Northwest69/Hamster/Processing/Hamster/application.linux-armv6hf/source/Hamster.pde

/* Hamster
 Software: 1.0.0
 Created by Peter Chau
 Start Date: August 9, 2015
 */

import processing.serial.*;
import controlP5.*; // For GUI interface

Serial myPort;

int index;

// GUI Declarations
ControlP5 myControls;
Slider dutySlider, degreeSlider;
Textfield attemptsTextfield, maxTextfield, probabilityTextfield;

int dutyCycle = 75;
public float rotateDegree = 30;
public String probabilities = "0.16667 0.16667 0.16667 0.16667 0.16667 0.16667";

int[] dutyCycleSlider = {
  250, 50
};
int[] rotateDegreeSlider = {
  300, 50
};

String attempts = "0";
String maxAttempts = "500";
int[] learningAttempt = {
  400, 100
};
int[] maxAttempt = {
  400, 50
};

int[] probability = {
  50, 250
};

int[] forward = {
  100, 50
};
int[] backward = {
  100, 150
};
int[] left = {
  50, 100
};
int[] right = {
  150, 100
};
int[] stop = {
  100, 100
};
int[] set = {
  400, 150
};
int[] reset = {
  400, 175
};
int[] save = {
  350, 250
};
int[] load = {
  400, 250
};

int foreground = #FF8686;
int background = #AA0000;
int active = #FF2929;
int canvas = #FFB2B2;

void setup() {
  String portName = Serial.list()[1]; //1 is bluetooth, 2 is serial
  myPort = new Serial(this, portName, 38400);
  myPort.clear();

  size(500, 350);
  background(100);

  /* GUI interface */
  myControls = new ControlP5(this);
  dutySlider = myControls.addSlider("dutyCycle", 0, 100, dutyCycle, dutyCycleSlider[0], dutyCycleSlider[1], 10, 137).setColorForeground(foreground).setColorActive(active).setColorBackground(background);
  degreeSlider = myControls.addSlider("rotateDegree", 1, 360, rotateDegree, rotateDegreeSlider[0], rotateDegreeSlider[1], 10, 137).setColorForeground(foreground).setColorActive(active).setColorBackground(background);
  maxTextfield = myControls.addTextfield("Max Attempts").setPosition(maxAttempt[0], maxAttempt[1]).setText(maxAttempts).setSize(50, 25).setAutoClear(false).setColorForeground(foreground).setColorActive(active).setColorBackground(background);
  attemptsTextfield = myControls.addTextfield("Current Attempts").setPosition(learningAttempt[0], learningAttempt[1]).setText(attempts).setSize(50, 25).setAutoClear(false).setColorForeground(foreground).setColorActive(active).setColorBackground(background);
  probabilityTextfield = myControls.addTextfield("Probabilities").setPosition(probability[0], probability[1]).setText(probabilities).setSize(275, 25).setAutoClear(false).setColorForeground(foreground).setColorActive(active).setColorBackground(background);

  myControls.addButton("Forward")
    .setPosition(forward[0], forward[1])
    .setSize(50, 50)
    .setValue(100).setColorForeground(foreground).setColorActive(active).setColorBackground(background)
    .addCallback(new CallbackListener() {
    public void controlEvent(CallbackEvent event) {
      if (event.getAction() == ControlP5.ACTION_PRESSED) {
        myPort.write("D 0\r");
        println("D 0\r");
      }
    }
  }
  );  
  myControls.addButton("Backward")
    .setPosition(backward[0], backward[1])
    .setSize(50, 50)
    .setValue(100).setColorForeground(foreground).setColorActive(active).setColorBackground(background)
    .addCallback(new CallbackListener() {
    public void controlEvent(CallbackEvent event) {
      if (event.getAction() == ControlP5.ACTION_PRESSED) {
        myPort.write("D 1\r");
        println("D 1\r");
      }
    }
  }
  ); 
  myControls.addButton("Right")
    .setPosition(right[0], right[1])
    .setSize(50, 50)
    .setValue(100).setColorForeground(foreground).setColorActive(active).setColorBackground(background)
    .addCallback(new CallbackListener() {
    public void controlEvent(CallbackEvent event) {
      if (event.getAction() == ControlP5.ACTION_PRESSED) {
        myPort.write("D 4\r");
        println("D 4\r");
      }
    }
  }
  ); 
  myControls.addButton("Left")
    .setPosition(left[0], left[1])
    .setSize(50, 50)
    .setValue(100).setColorForeground(foreground).setColorActive(active).setColorBackground(background)
    .addCallback(new CallbackListener() {
    public void controlEvent(CallbackEvent event) {
      if (event.getAction() == ControlP5.ACTION_PRESSED) {
        myPort.write("D 5\r");
        println("D 5\r");
      }
    }
  }
  ); 
  myControls.addButton("Stop")
    .setPosition(stop[0], stop[1])
    .setSize(50, 50)
    .setValue(100).setColorForeground(foreground).setColorActive(active).setColorBackground(background)
    .addCallback(new CallbackListener() {
    public void controlEvent(CallbackEvent event) {
      if (event.getAction() == ControlP5.ACTION_PRESSED) {
        myPort.write("D 6\r");
        println("D 6\r");
      }
    }
  }
  ); 
  myControls.addButton("Set")
    .setPosition(set[0], set[1])
    .setSize(50, 25)
    .setValue(0).setColorForeground(foreground).setColorActive(active).setColorBackground(background)
    .addCallback(new CallbackListener() {
    public void controlEvent(CallbackEvent event) {
      if (event.getAction() == ControlP5.ACTION_PRESSED) {
        myPort.write("S " + str(dutyCycle) + "\r");
        println("S " + dutyCycle + "\r");  
        myPort.write("T " + str(rotateDegree) + "\r");
        println("T " + rotateDegree + "\r");
        maxAttempts = myControls.get(Textfield.class, "Max Attempts").getText();
        myPort.write("L " + maxAttempts + "\r");
        println("L " + maxAttempts + "\r");
        probabilities = myControls.get(Textfield.class, "Probabilities").getText();
        //myPort.write("P " + probabilities + "\r");
        //println("P " + probabilities + "\r");      
    }
    }
  }
  );  
  myControls.addButton("Reset")
    .setPosition(reset[0], reset[1])
    .setSize(50, 25)
    .setValue(0).setColorForeground(foreground).setColorActive(active).setColorBackground(background)
    .addCallback(new CallbackListener() {
    public void controlEvent(CallbackEvent event) {
      if (event.getAction() == ControlP5.ACTION_PRESSED) {
        myPort.write("R\r");
        println("R\r");
        attempts = "0";
        dutyCycle = 75;
        rotateDegree = 30;
        maxAttempts = "500";
        probabilities = "0.16667 0.16667 0.16667 0.16667 0.16667 0.16667";
        attemptsTextfield.setValue(attempts);
        dutySlider.setValue(dutyCycle);
        degreeSlider.setValue(rotateDegree);
        maxTextfield.setValue(maxAttempts);
        probabilityTextfield.setValue(probabilities);
      }
    }
  }
  );
    myControls.addButton("Save")
    .setPosition(save[0], save[1])
    .setSize(50, 25)
    .setValue(0).setColorForeground(foreground).setColorActive(active).setColorBackground(background)
    .addCallback(new CallbackListener() {
    public void controlEvent(CallbackEvent event) {
      if (event.getAction() == ControlP5.ACTION_PRESSED) {
        String[] loadFile = loadStrings("probabilities.txt");
        String[] saveFile = splice(loadFile, probabilities, loadFile.length);
        saveStrings("probabilities.txt", saveFile);
        println("Probabilities Saved!");
        
      }
    }
  }
  );
      myControls.addButton("Load")
    .setPosition(load[0], load[1])
    .setSize(50, 25)
    .setValue(0).setColorForeground(foreground).setColorActive(active).setColorBackground(background)
    .addCallback(new CallbackListener() {
    public void controlEvent(CallbackEvent event) {
      if (event.getAction() == ControlP5.ACTION_PRESSED) {
        String[] loadFile = loadStrings("probabilities.txt");
        index = loadFile.length-1;
        if (index >= 0){
        probabilities = loadFile[index];
        myPort.write("P " + probabilities + "\r");
                probabilityTextfield.setValue(probabilities);
                println("Probabilities Loaded!");
        println("P " + probabilities + "\r"); 
        } else {
println("Probabilities could not be loaded");

        }
      }
    }
  }
      );
}

void draw() {
  background(canvas);

  /* Send command if keyboard button pressed */
  if (keyPressed == true) {
    if (key == CODED) {
      if (keyCode == UP) {
        myPort.write("D 0\r");
        println("D 0\r");
      } else if (keyCode == DOWN) {
        myPort.write("D 1\r");
        println("D 1\r");
      } else if (keyCode == RIGHT) {
        myPort.write("D 4\r");
        println("D 4\r");
      } else if (keyCode == LEFT) {
        myPort.write("D 5\r");
        println("D 5\r");
      } else if (keyCode == CONTROL) {
        myPort.write("D 6\r");
        println("D 6\r");
      }
    } else if (key == ENTER) {
      myPort.write("S " + str(dutyCycle) + "\r");
      println("S " + dutyCycle + "\r");  
      myPort.write("T " + str(rotateDegree) + "\r");
      println("T " + rotateDegree + "\r");
      maxAttempts = myControls.get(Textfield.class, "Max Attempts").getText();
      myPort.write("L " + maxAttempts + "\r");
      println("L " + maxAttempts + "\r");
      probabilities = myControls.get(Textfield.class, "Probabilities").getText();
      // myPort.write("P " + probabilities + "\r");
      //  println("P " + probabilities + "\r");   
    }
  }

  while (myPort.available () > 0) {
    String current = myPort.readStringUntil('\n');
    // if you got any bytes other than the linefeed:
    if (current != null) {
      current = trim(current);
      String[] currentString = split(current, " ");
      if (currentString[0].equals("C")) {
        attempts = currentString[1];
        attemptsTextfield.setValue(attempts);
        //println(currentString[0]);
      }
      if (currentString[0].equals("P")) {
        currentString = subset(currentString, 1);
        probabilities = join(currentString, " ");
        probabilityTextfield.setValue(probabilities);
        println(probabilities);
        }
    }
  }
}
